Maksym-UA/Gate_reed_control_2.4ghz/Diagrams/architect-diagram-pop.png

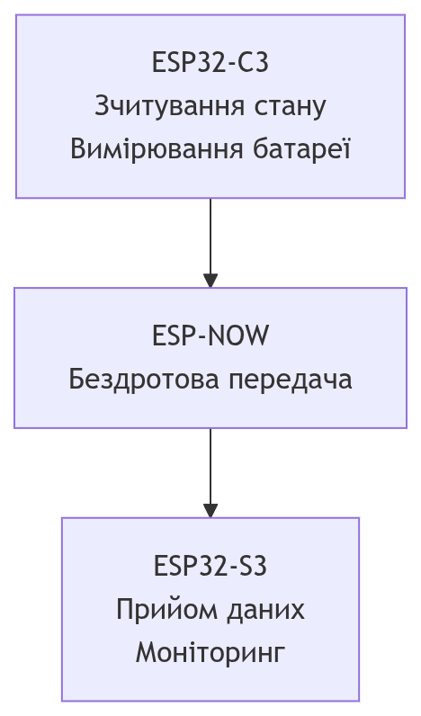
Diagrams/architect-diagram-pop.png
