Maksym-UA/Gate_reed_control_2.4ghz/KiCad/Gate reed.kicad_pcb

## KiCad design schematics/Tank/Tank.kicad_sch

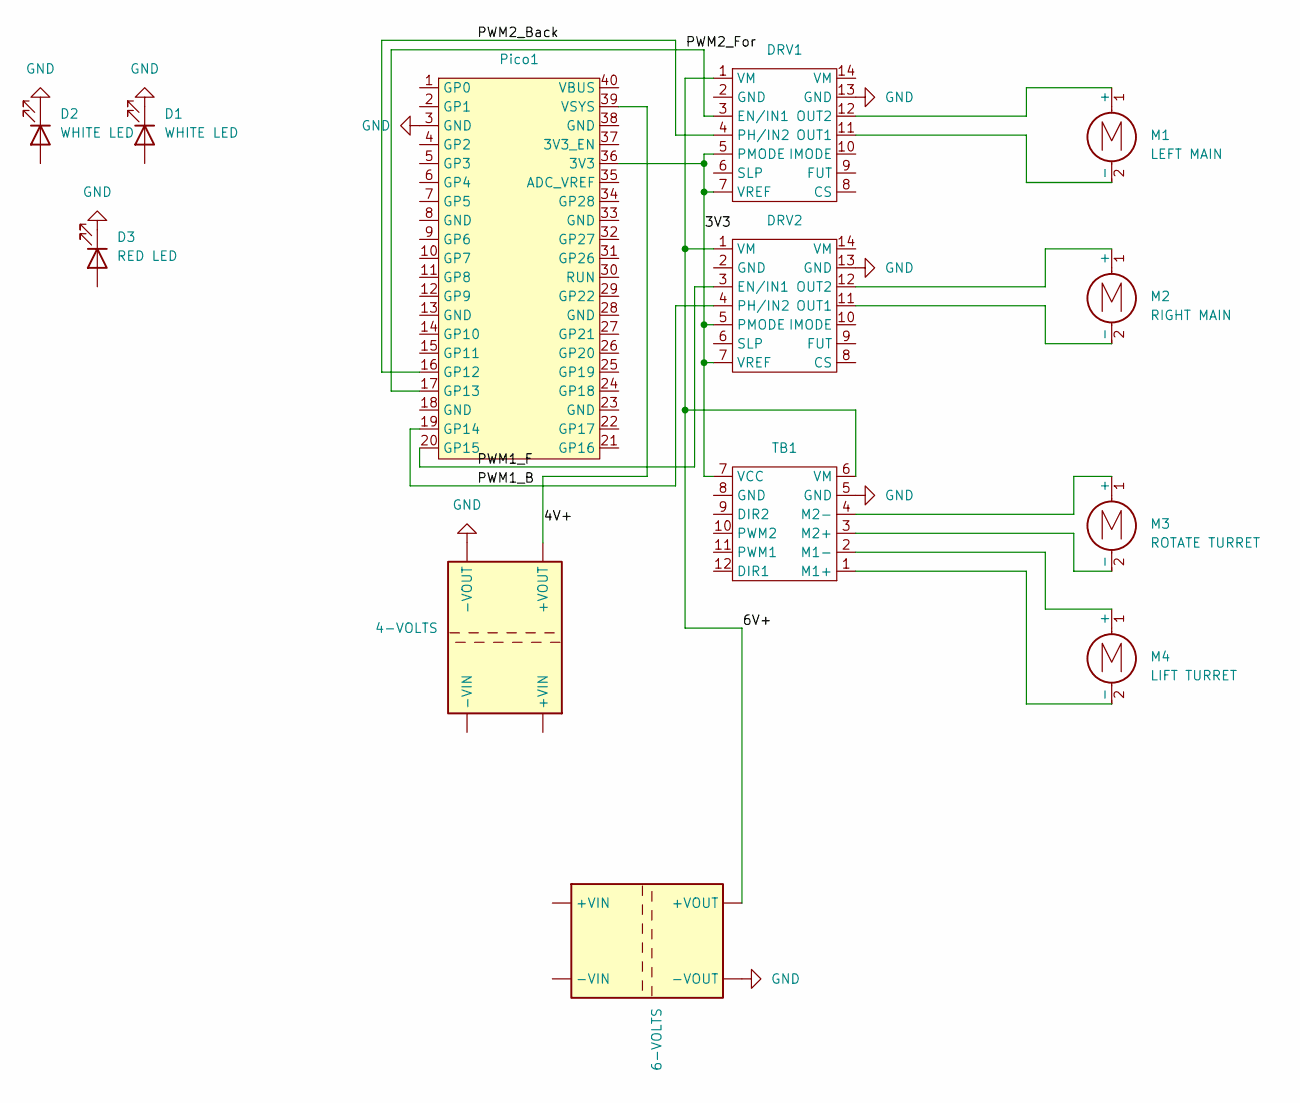
[picture p9: schematic Tank.kicad_sch]

Parts:
4-VOLTS, 6-VOLTS: (no value)
D1, D2: WHITE LED
D3: RED LED
DRV1, DRV2: (no value)
M1: LEFT MAIN
M2: RIGHT MAIN
M3: ROTATE TURRET
M4: LIFT TURRET
Pico1: (no value)
TB1: (no value)

Connections:
3V3: DRV1.5 (PMODE), DRV1.7 (VREF), DRV2.5 (PMODE), DRV2.7 (VREF), Pico1.36 (3V3), TB1.7 (VCC)
4V+: 4-VOLTS.4 (+VOUT), Pico1.39 (VSYS)
6V+: 6-VOLTS.4 (+VOUT), DRV1.1 (VM), DRV2.1 (VM), TB1.6 (VM)
GND: 4-VOLTS.3 (-VOUT), 6-VOLTS.3 (-VOUT), D1.1 (K), D2.1 (K), D3.1 (K), DRV1.13 (GND), DRV2.13 (GND), Pico1.3 (GND), TB1.5 (GND)
unnamed: DRV1.11 (OUT1), M1.2 (-)
unnamed: DRV1.12 (OUT2), M1.1 (+)
unnamed: DRV2.11 (OUT1), M2.2 (-)
unnamed: DRV2.12 (OUT2), M2.1 (+)
unnamed: M3.1 (+), TB1.4 (M2-)
unnamed: M3.2 (-), TB1.3 (M2+)
unnamed: M4.1 (+), TB1.2 (M1-)
unnamed: M4.2 (-), TB1.1 (M1+)
PWM1_B: DRV2.4 (PH/IN2), Pico1.19 (GP14)
PWM1_F: DRV2.3 (EN/IN1), Pico1.20 (GP15)
PWM2_Back: DRV1.4 (PH/IN2), Pico1.16 (GP12)
PWM2_For: DRV1.3 (EN/IN1), Pico1.17 (GP13)
