Maksym-UA/Gate_reed_control_2.4ghz/ESP32-C3/include/application.h

#pragma once

#include <stdint.h>

#include "driver/gpio.h"

namespace app {

    struct Config {
        gpio_num_t sensorPin;
        gpio_num_t ledPin;
        gpio_num_t voltagePin;
        int debounceMs;
        int loopDelayMs;
    };

    void init(const Config &config);
    void run();

}  // namespace app
